zxlzzz/LingTouchCompanion/BrailleModule_Video/MotionPreview/assets/Base.png

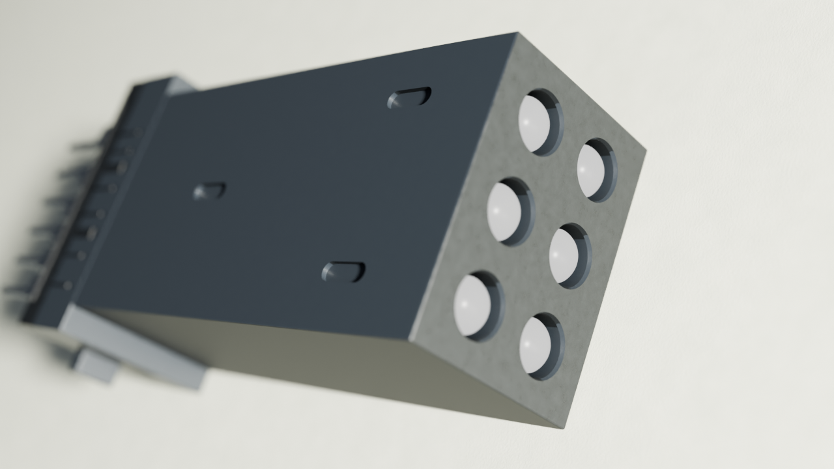
BrailleModule_Video/MotionPreview/assets/Base.png
