zxlzzz/LingTouchCompanion/3mf/PCB/PCB_SW_INNER4_2026-10-07.png

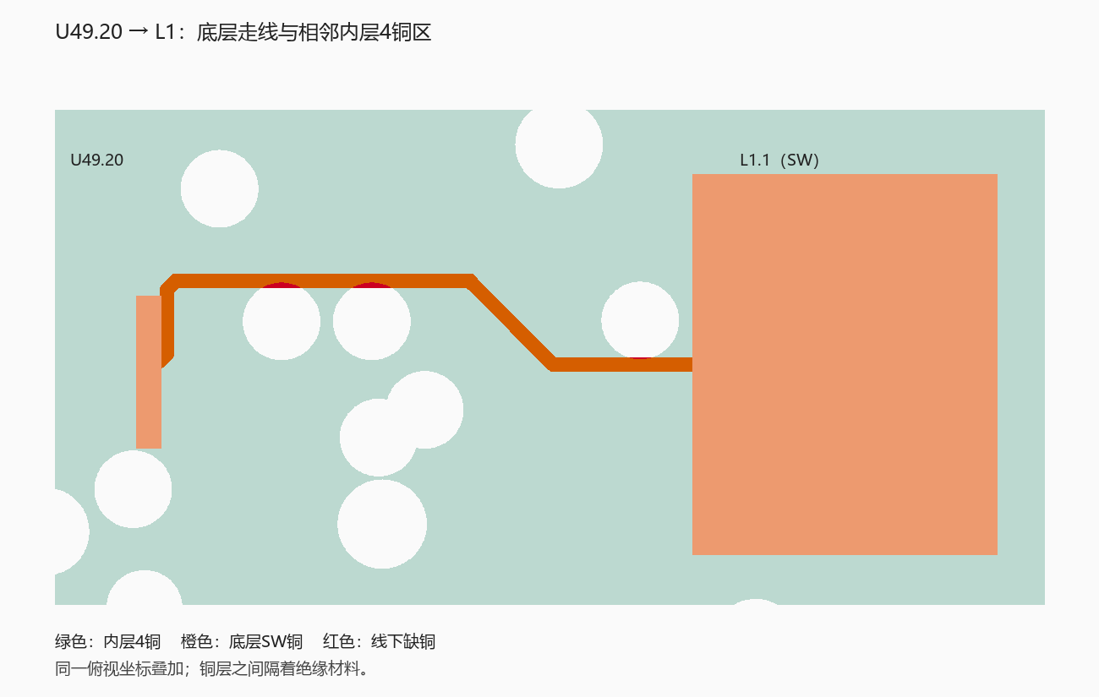
3mf/PCB/PCB_SW_INNER4_2026-10-07.png
