zxlzzz/LingTouchCompanion/BrailleModule/inputs/Touchpoint_Reference.jpg

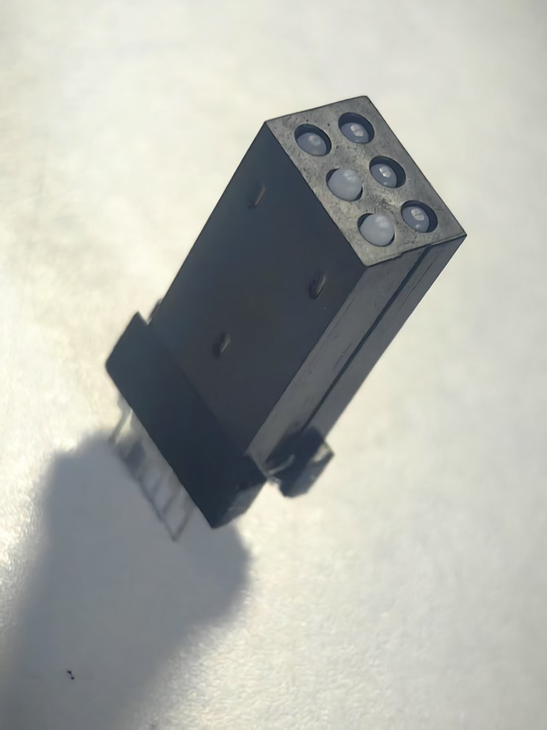
BrailleModule/inputs/Touchpoint_Reference.jpg
