zxlzzz/LingTouchCompanion/BrailleModule/Preview.png

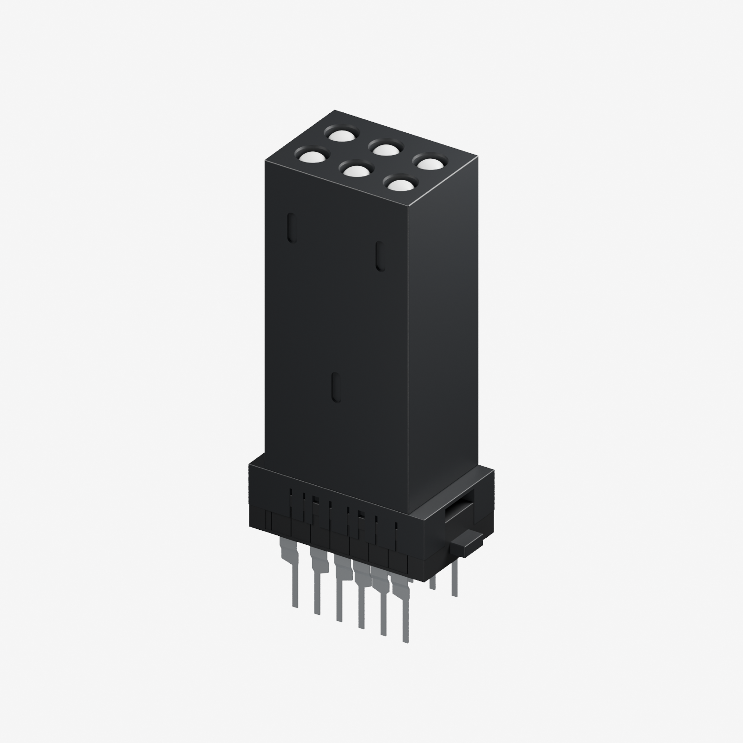
BrailleModule/Preview.png
