zxlzzz/LingTouchCompanion/BrailleModule/Preview_Dots.png

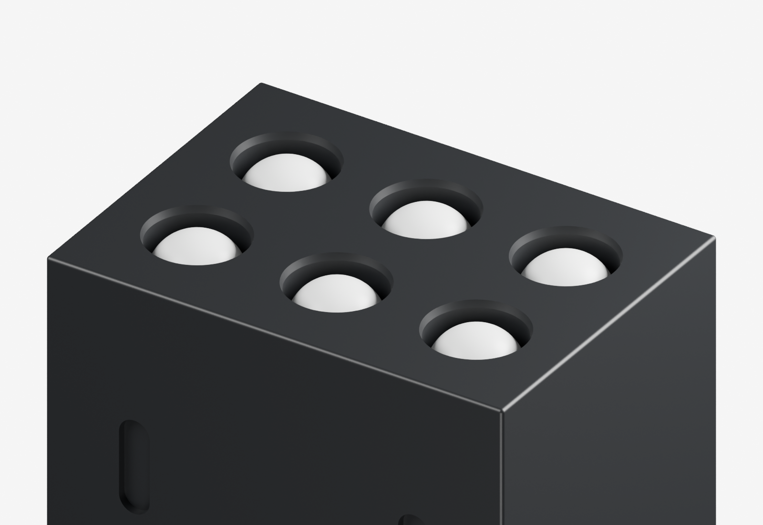
BrailleModule/Preview_Dots.png
