zxlzzz/LingTouchCompanion/BrailleModule/Preview_Top.png

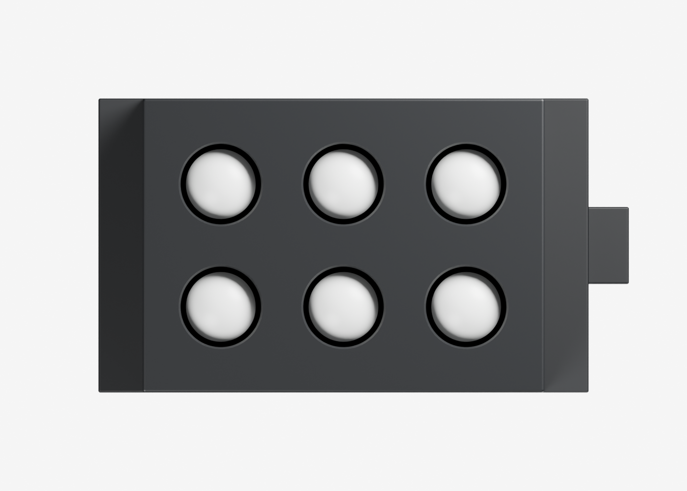
BrailleModule/Preview_Top.png
