zxlzzz/LingTouchCompanion/BrailleModule_Video/ArrayPreview/assets/textures/MouldDetail.png

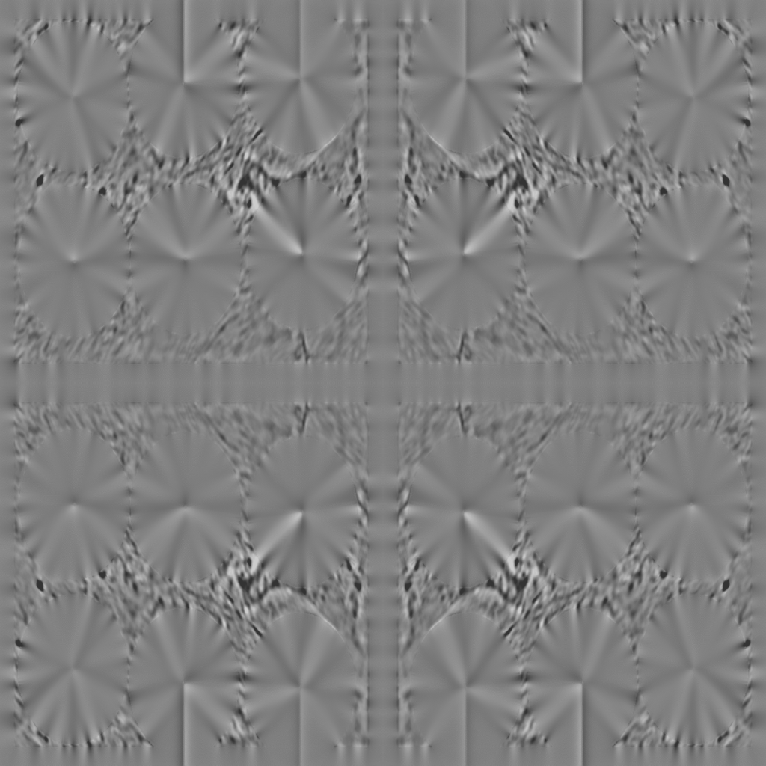
BrailleModule_Video/ArrayPreview/assets/textures/MouldDetail.png
