zxlzzz/LingTouchCompanion/BrailleModule_Video/ArrayPreview/assets/textures/Plastic003/Plastic003_2K-PNG_Color.png

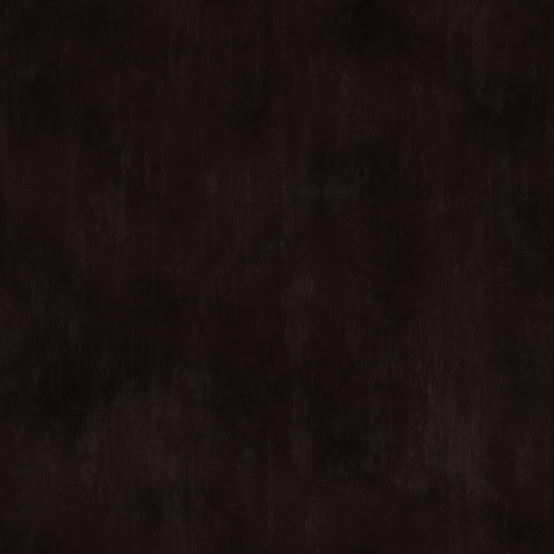
BrailleModule_Video/ArrayPreview/assets/textures/Plastic003/Plastic003_2K-PNG_Color.png
