zxlzzz/LingTouchCompanion/BrailleModule_Video/ArrayPreview/PinCloseup.png

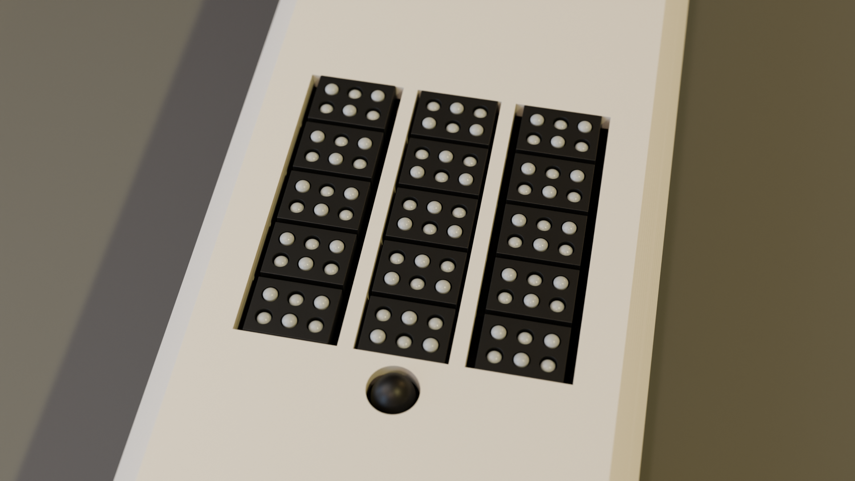
BrailleModule_Video/ArrayPreview/PinCloseup.png
