zxlzzz/LingTouchCompanion/BrailleModule_Video/ArrayPreview/SwitchPreview.png

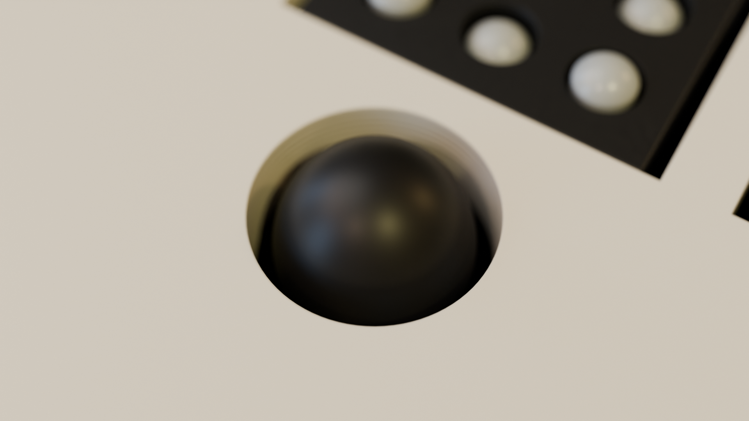
BrailleModule_Video/ArrayPreview/SwitchPreview.png
