zxlzzz/LingTouchCompanion/BrailleModule_Video/MotionPreview/assets/dot_1.png

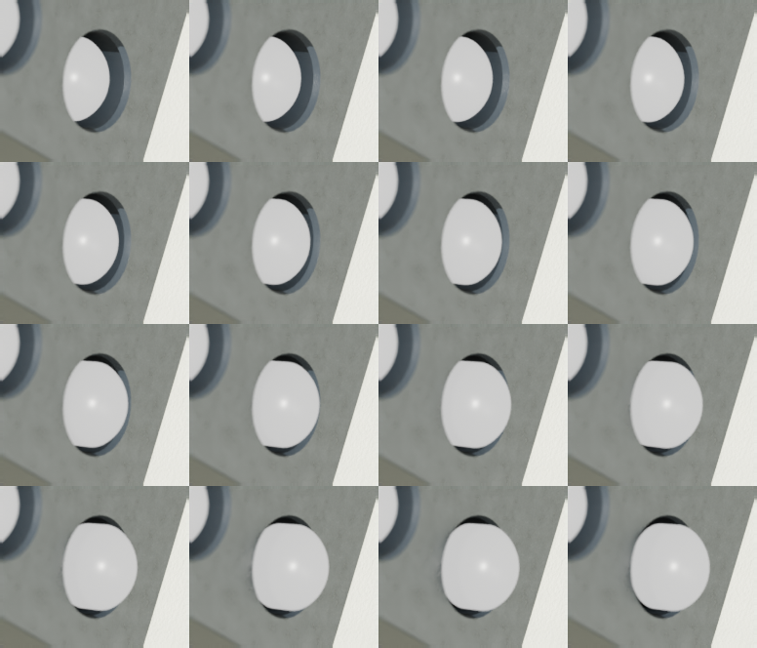
BrailleModule_Video/MotionPreview/assets/dot_1.png
