zxlzzz/LingTouchCompanion/BrailleModule_Video/MotionPreview/assets/dot_3.png

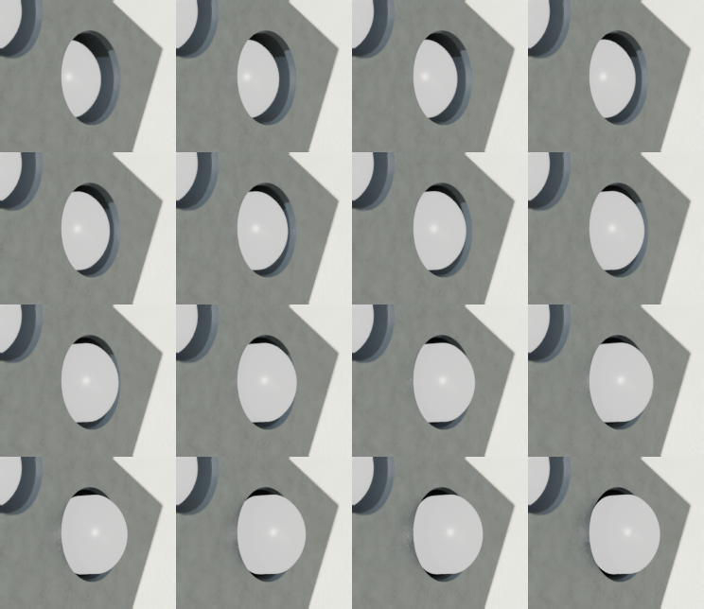
BrailleModule_Video/MotionPreview/assets/dot_3.png
