zxlzzz/LingTouchCompanion/BrailleModule_Video/MotionPreview/assets/dot_4.png

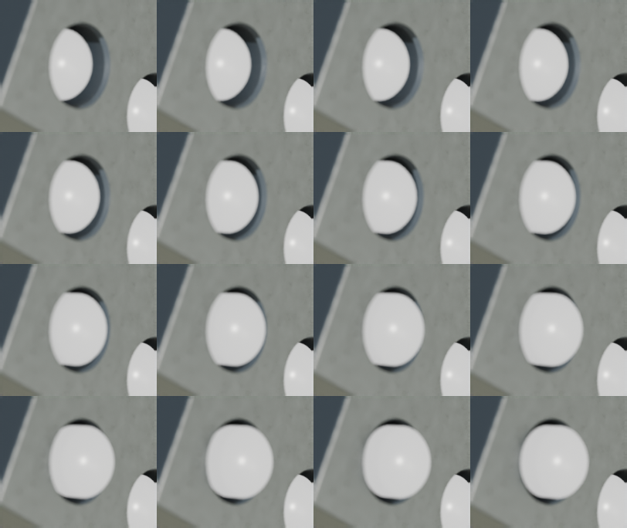
BrailleModule_Video/MotionPreview/assets/dot_4.png
