zxlzzz/LingTouchCompanion/BrailleModule_Video/MotionPreview/assets/dot_5.png

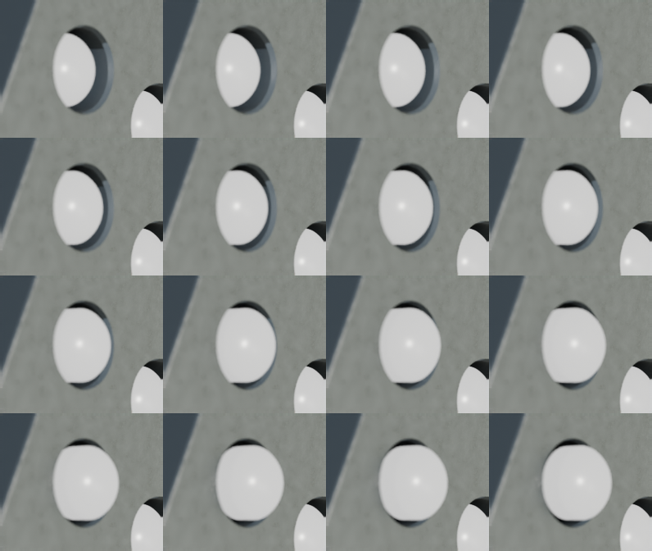
BrailleModule_Video/MotionPreview/assets/dot_5.png
