zxlzzz/LingTouchCompanion/BrailleModule_Video/MotionPreview/assets/dot_6.png

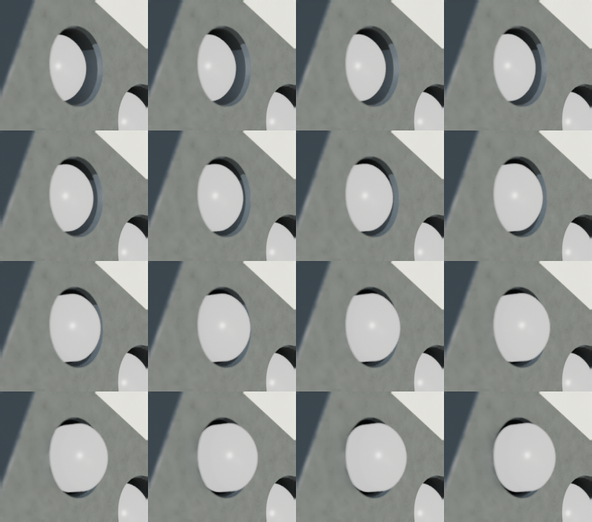
BrailleModule_Video/MotionPreview/assets/dot_6.png
