zxlzzz/LingTouchCompanion/BrailleModule_Video/MotionPreview/PinPreview.jpg

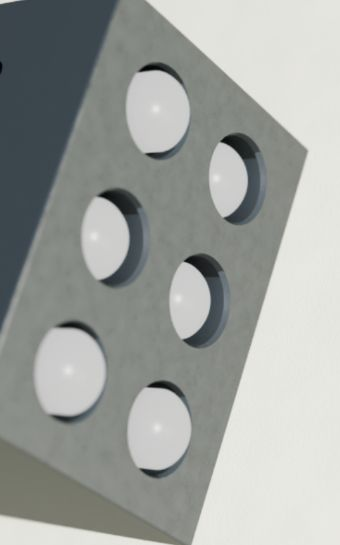
BrailleModule_Video/MotionPreview/PinPreview.jpg
