zxlzzz/LingTouchCompanion/BrailleModule_Video/MotionPreview/Preview.jpg

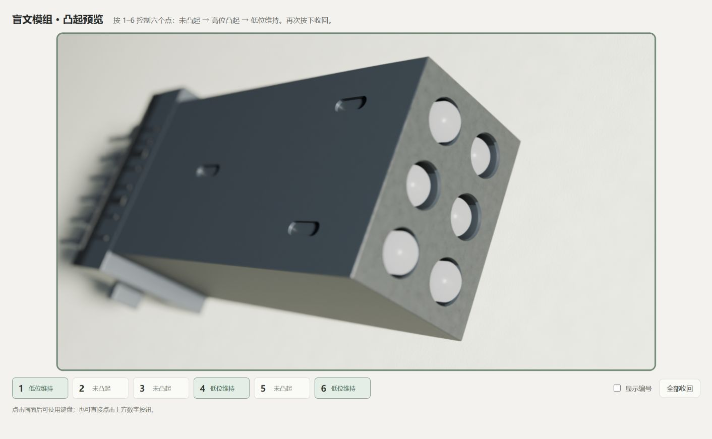
BrailleModule_Video/MotionPreview/Preview.jpg
