zxlzzz/LingTouchCompanion/BrailleModule_Video/PhotoStudy/ReferenceStudy.png

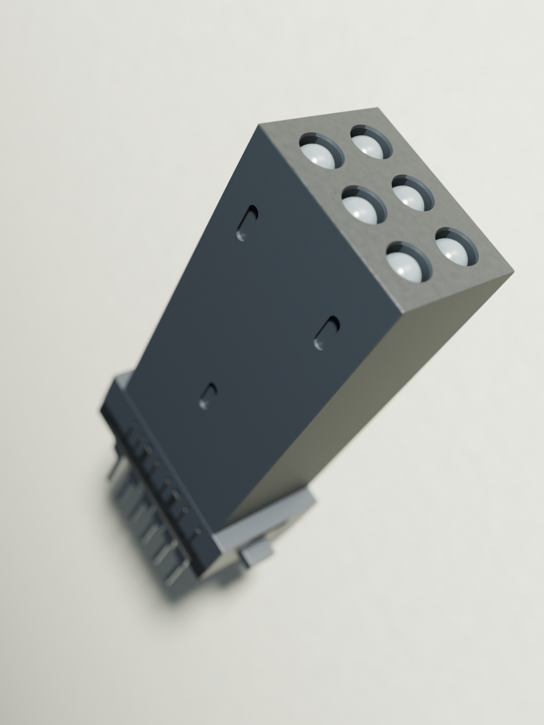
BrailleModule_Video/PhotoStudy/ReferenceStudy.png
