zxlzzz/LingTouchCompanion/vision/1.jpg

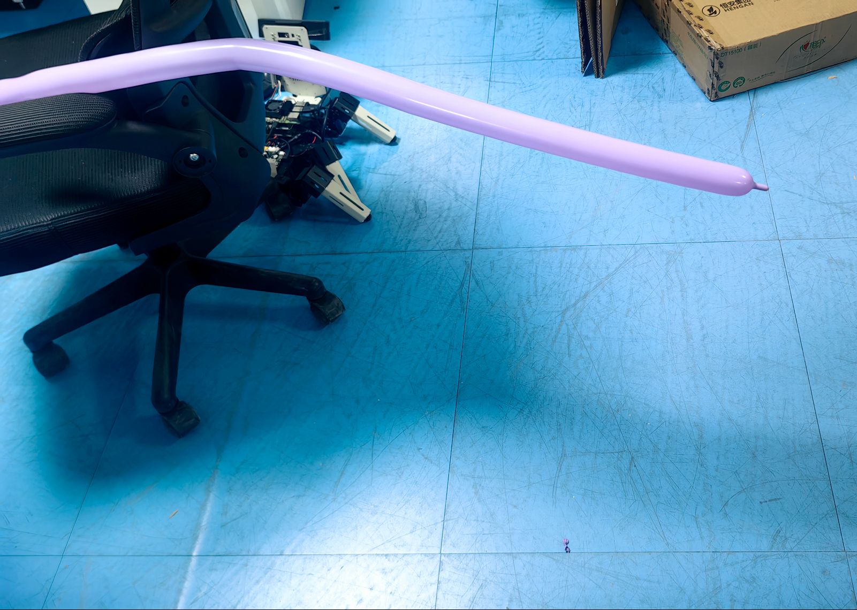
vision/1.jpg
