zxlzzz/LingTouchCompanion/vision/2.jpg

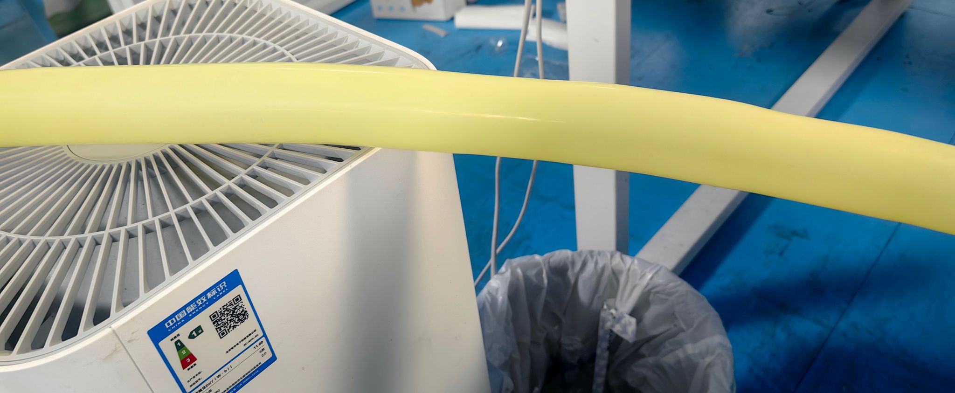
vision/2.jpg
