zxlzzz/LingTouchCompanion/3mf/PCB/PCB_MEASURE_MAP_2026-10-07.png

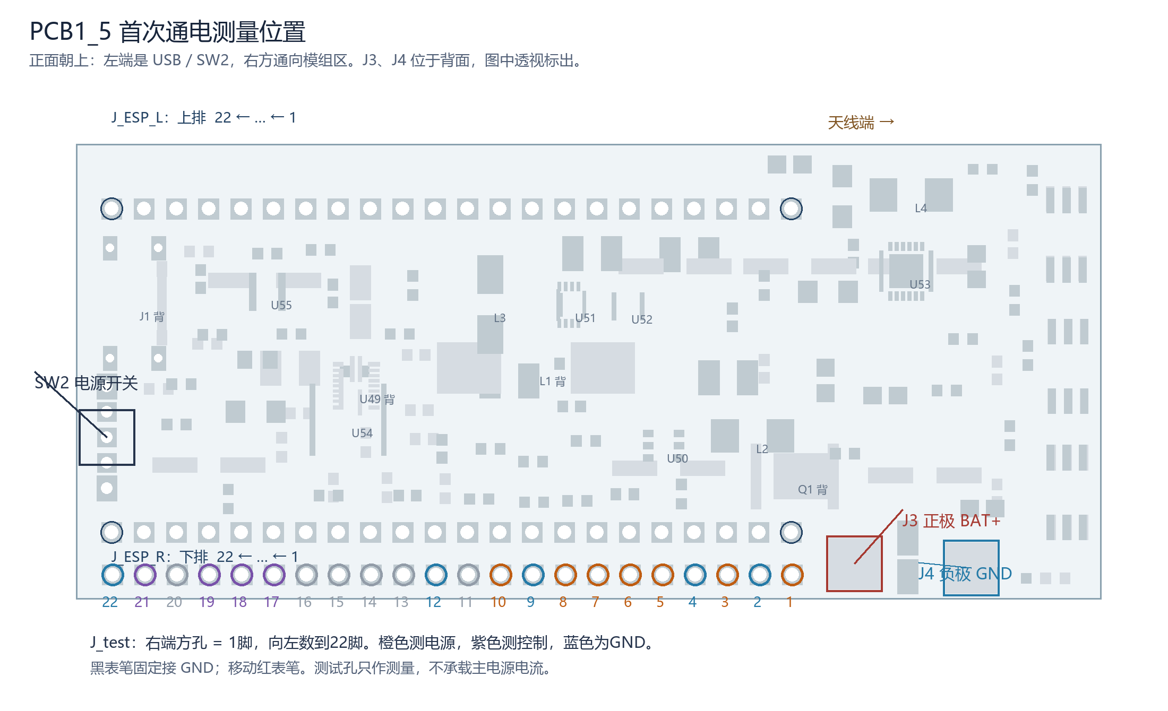
3mf/PCB/PCB_MEASURE_MAP_2026-10-07.png
