zxlzzz/LingTouchCompanion/PCB_REDESIGN_2026-10-08/test_placement.png

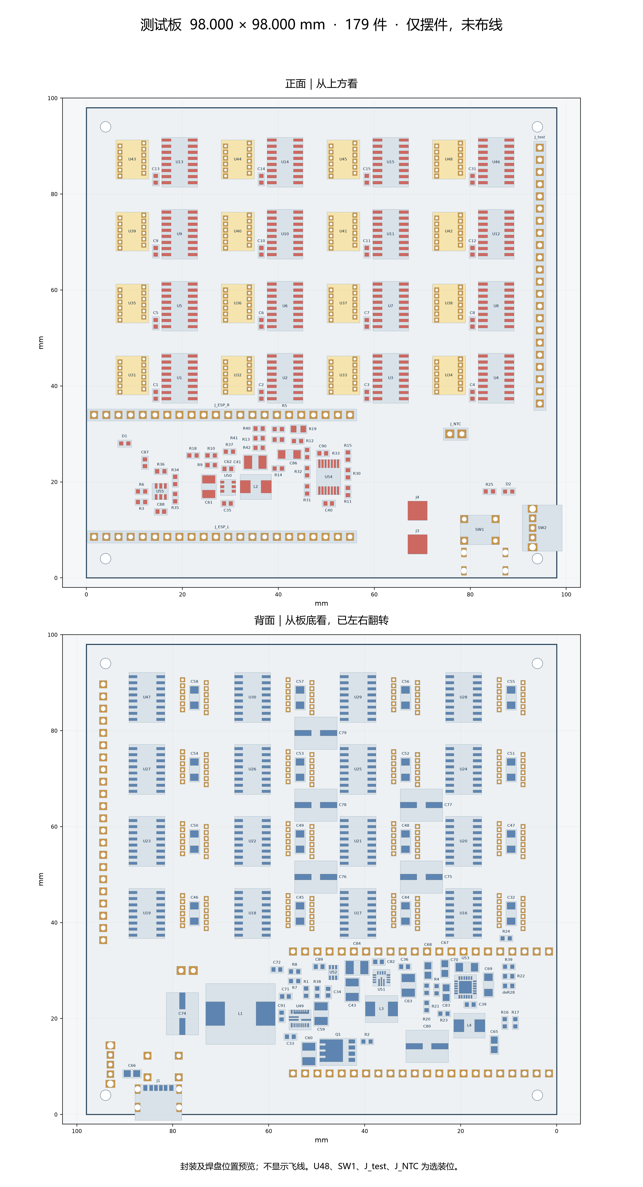
PCB_REDESIGN_2026-10-08/test_placement.png
